thurstinn/RP5-Console/Hardware/3D CAD/SLA Resin/Ant_Cover.step

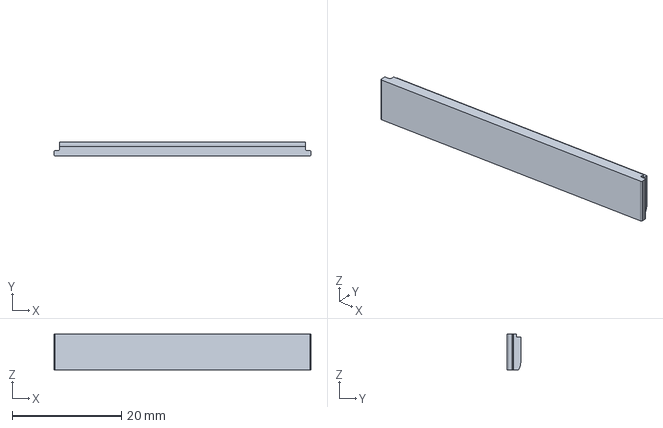
[picture p20: CAD file, 2025-03-01]
Hardware/3D CAD/SLA Resin/Ant_Cover.step
47.0 x 2.50 x 6.50 mm
